izzy84075/fx2grok/hardware/fx2grok-cube/0.1/fx2grok-cube.sch

## KiCad design hardware/fx2grok-cube/0.1/fx2grok-cube.sch (2017-07-09)

Schematic: fx2grok-cube.sch

Parts:
C1, C14: 1uF; SM0402
C2, C5, C7, C8, C10, C11, C12, C13, C15: 100nF; SM0402
C3, C6, C16: 2.2uF; SM0402
C4, C9: 12pF; SM0402
D1: LED1; SM0402
IC1: CY7C68013A-56; QFN56
P1, P2: CONN_01X05; CONN-5x1-SMD-127MM
R1: 100K; SM0402
R2, R3, R4, R5: 2K7; SM0402
U1: MICRO-USB-B-SMD
U2: MIC5319; SOT23-5
Y1: Crystal; ABM11

Notes on the sheet:
5x2 1.27mm pin header (5 pins per PCB side)
Kicad-internal stuff, ignore
LED
RESET# is tied to VCC via 2K7 and 1uF
WAKEUP is tied to VCC
24MHz crystal
3.3V voltage regulator
USB
RESERVED must be tied to GND
2.2uF/100nF bypass capacitors for all AVCC pins
100nF bypass capacitors for all VCC pins
I2C pullups
